wolf-yuan-6115/smolpad/firmware/keymaps/default/bitmaps.h

#pragma once

#include QMK_KEYBOARD_H

extern const uint8_t PROGMEM game_text[512];
extern const uint8_t PROGMEM chat_text[512];
extern const uint8_t PROGMEM media_text[512];
extern const uint8_t PROGMEM aux_text[512];
extern const uint8_t PROGMEM vol_down[512];
extern const uint8_t PROGMEM vol_up[512];
extern const uint8_t PROGMEM prev_logo[512];
extern const uint8_t PROGMEM next_logo[512];
extern const uint8_t PROGMEM playpause_logo[512];
extern const uint8_t PROGMEM smolpad_logo[512];
extern const uint8_t PROGMEM next_space_logo[512];
extern const uint8_t PROGMEM prev_space_logo[512];
extern const uint8_t PROGMEM copied_logo[512];
extern const uint8_t PROGMEM selected_logo[512];
extern const uint8_t PROGMEM pasted_logo[512];
